mva-one/Weight-O-Matic/Weight-O-Matic_HW/Weight-O-Matic_HW.kicad_sch

## KiCad design Weight-O-Matic_HW/Weight-O-Matic_HW.kicad_sch (2024-09-28)

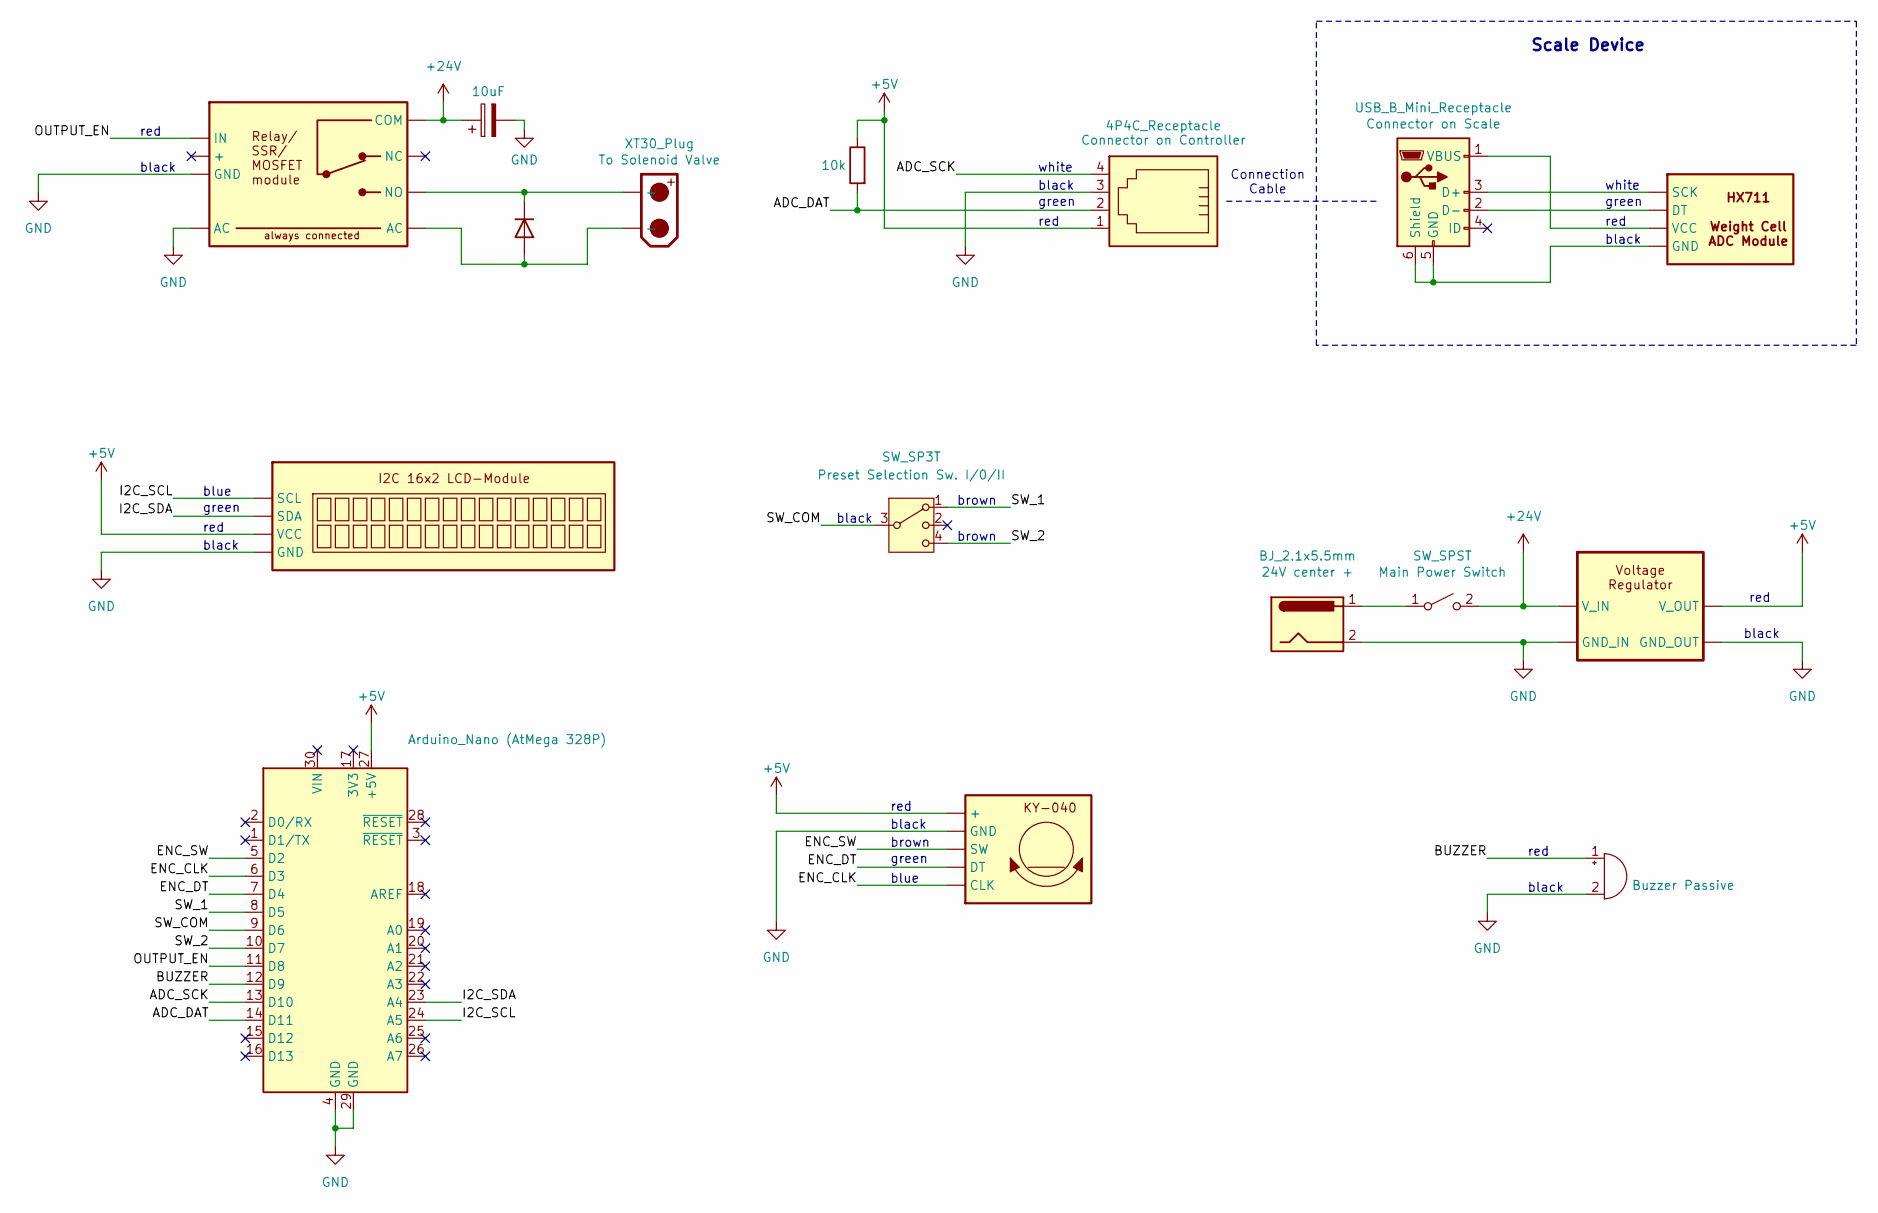
[picture p9: schematic Weight-O-Matic_HW.kicad_sch]

Parts:
A1: Arduino_Nano (AtMega 328P); Arduino_Nano
BZ1: Buzzer Passive
C1: 10uF
D1: (no value)
J1: XT30_Plug
J2: BJ_2.1x5.5mm
J5: USB_B_Mini_Receptacle
J6: 4P4C_Receptacle
M1, M2, M3, M4, M5: (no value)
R1: 10k
SW2: SW_SPST
SW3: SW_SP3T

Connections:
+5V: A1.27 (+5V), J6.1, M1., M2., M3., R1.1
+24V: C1.1, M1., M4., SW2.2 (B)
ADC_DAT: A1.14 (D11), J6.2, R1.2
ADC_SCK: A1.13 (D10), J6.4
BUZZER: A1.12 (D9), BZ1.1 (+)
ENC_CLK: A1.6 (D3), M3.
ENC_DT: A1.7 (D4), M3.
ENC_SW: A1.5 (D2), M3.
GND: A1.4 (GND), A1.29 (GND), BZ1.2 (-), C1.2, J2.2, J6.3, M1., M2., M3., M4.
I2C_SCL: A1.24 (A5), M2.
I2C_SDA: A1.23 (A4), M2.
unnamed: D1.1 (K), J1., M4.
unnamed: D1.2 (A), J1., M4.
unnamed: J2.1, SW2.1 (A)
unnamed: J5.1 (VBUS), M5.
unnamed: J5.2 (D-), M5.
unnamed: J5.3 (D+), M5.
unnamed: J5.5 (GND), J5.6 (Shield), M5.
OUTPUT_EN: A1.11 (D8), M4.
SW_1: A1.8 (D5), SW3.1
SW_2: A1.10 (D7), SW3.4
SW_COM: A1.9 (D6), SW3.3

Notes on the sheet:
blue
black
white
green
Connection Cable
red
brown
Scale Device
